IstiaMecatroniqueClub/Power_Board/documentation/html/output_8h__dep__incl.png

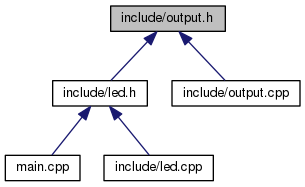
documentation/html/output_8h__dep__incl.png
