IstiaMecatroniqueClub/Power_Board/documentation/html/pin_8h__dep__incl.png

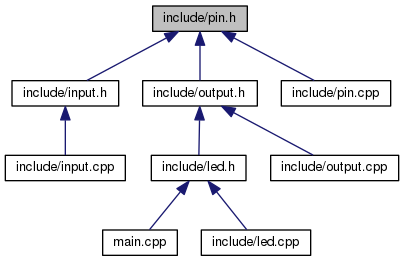
documentation/html/pin_8h__dep__incl.png
